bajraan/Sienkiewicz_LED/__QR/Github.Sienkiewicz_LED.png

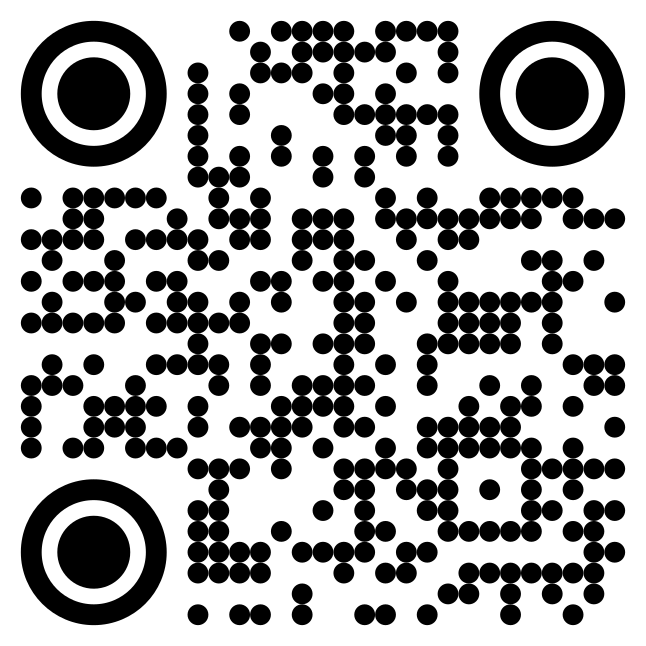
__QR/Github.Sienkiewicz_LED.png
