bajraan/Sienkiewicz_LED/HTML/images/cat_pdf_drill_map_Sienkiewicz_LED-PTH_drill_map.png

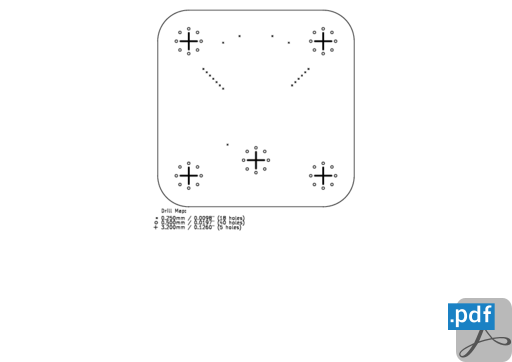
HTML/images/cat_pdf_drill_map_Sienkiewicz_LED-PTH_drill_map.png
