bajraan/Sienkiewicz_LED/HTML/images/cat_png_3d_viewer_angled_top_Sienkiewicz_LED-angled_top.png

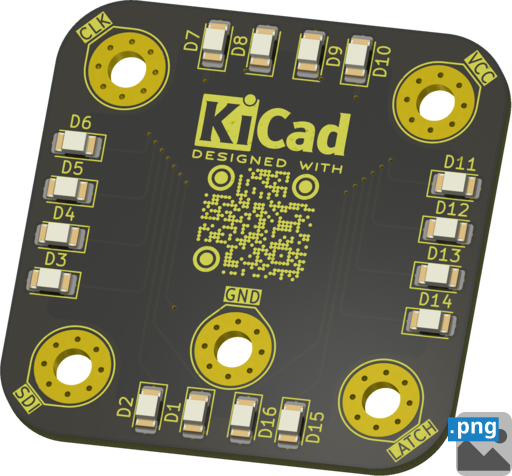
HTML/images/cat_png_3d_viewer_angled_top_Sienkiewicz_LED-angled_top.png
