bajraan/Sienkiewicz_LED/HTML/images/cat_png_3d_viewer_top_Sienkiewicz_LED-top.png

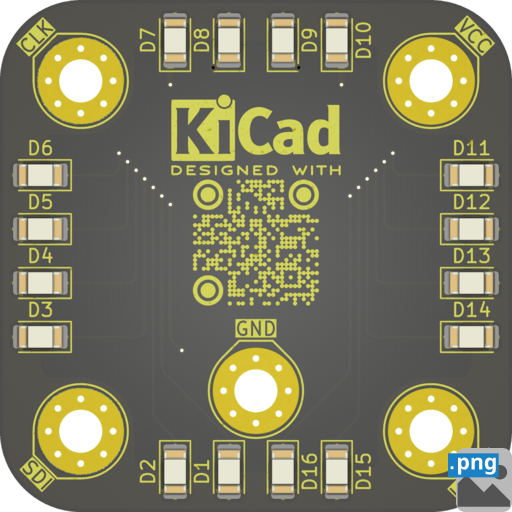
HTML/images/cat_png_3d_viewer_top_Sienkiewicz_LED-top.png
