bajraan/Sienkiewicz_LED/Manufacturing/Assembly/Sienkiewicz_LED-assembly.pdf

# 3ART13 LED Assembly Document

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

BaJRan imgaginary industries

Top/Bottom View

# Top Assembly (Scale 1:1)

# 3ART13 LED Assembly Document


# Bottom Assembly (Scale 1:1)

# 3ART13 LED Assembly Document

Git; Hash:; c7cddf3; Comments:; Sheet Path:; Sheet Title:; File Name:; 3ART13 LED; Sienkiewicz; Company:; CHECKED; Variant:; Board Name:; Sienkiewicz_LED.kicad_pcb; Paweł Baran; Designer:; Reviewer:; Project Name:; Date:; 2.1.1+ (Unreleased); Revision:; Size:; Sheet:; STP16CP05M; 3ART13; SIENKIEWICZ; imaginary industries; BaJRan

BaJRan imgaginary industries

Bottom Assembly (Scale 1:1)
