bajraan/Sienkiewicz_LED/Manufacturing/Fabrication/Sienkiewicz_LED-fabrication-1.pdf

# Top Fabrication (Scale 1:1)

# 3ART13 LED Fabrication Document

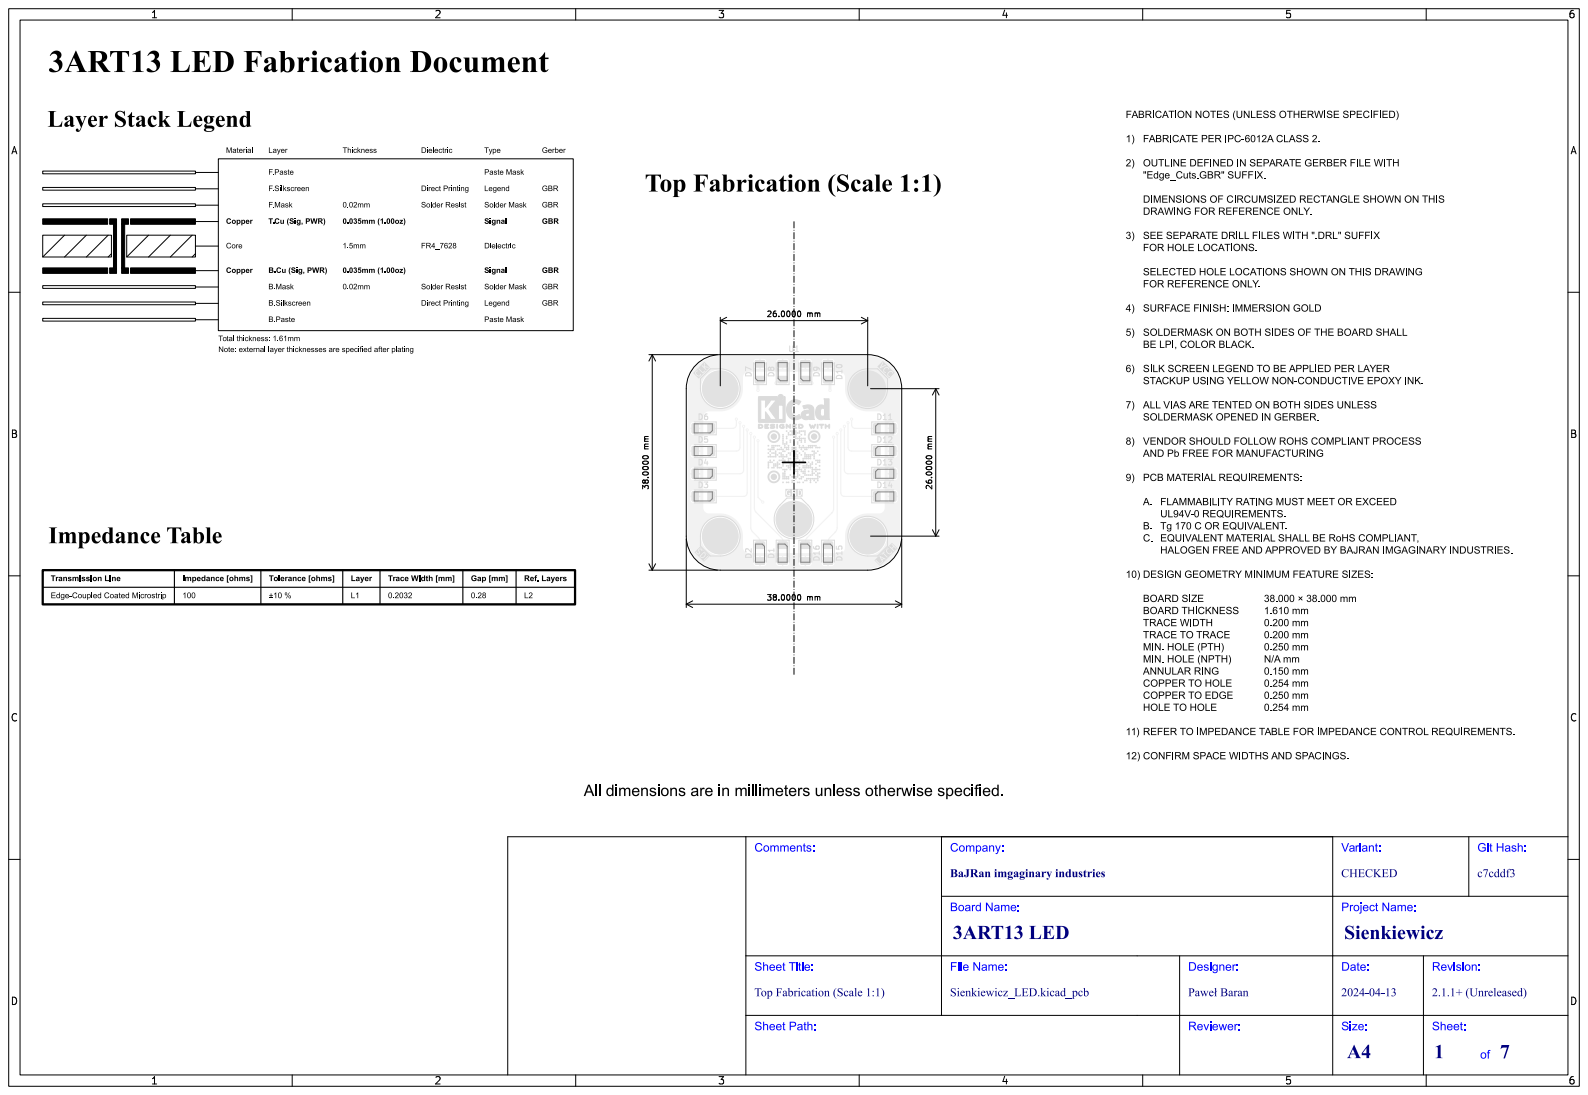
[picture p25: page 1]
