bajraan/Sienkiewicz_LED/Manufacturing/Fabrication/Sienkiewicz_LED-fabrication-3.pdf

# Drill Drawing L1 - L2 (Scale 1:1)

# 3ART13 LED Fabrication Document

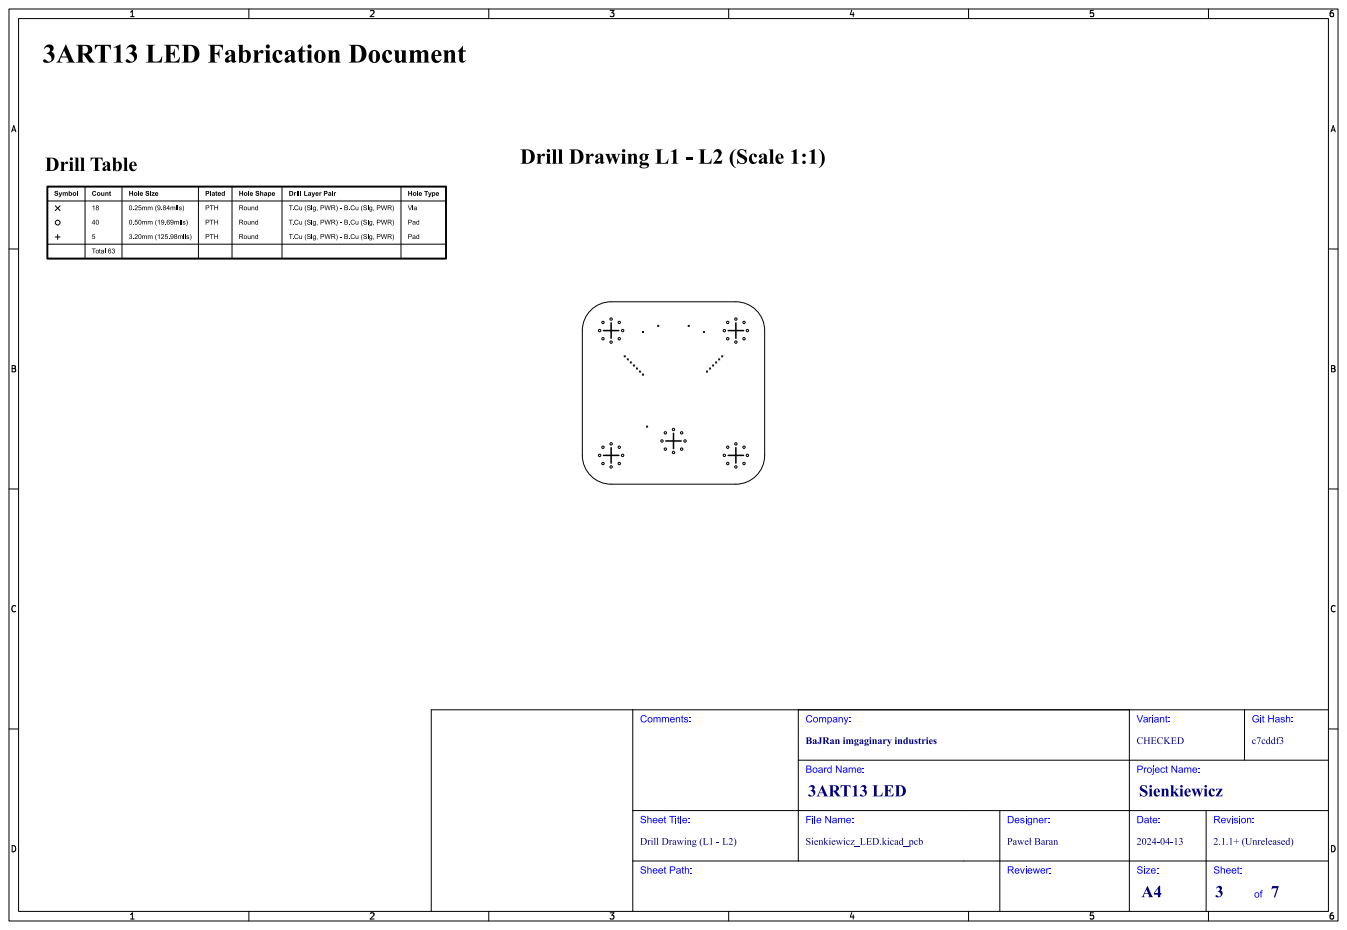
[picture p27: page 1]
Git; Hash:; c7cddf3; Comments:; Drill Drawing (L1 - L2); Sheet Path:; Sheet Title:; File Name:; 3ART13 LED; Sienkiewicz; Company:; CHECKED; Variant:; Board Name:; Sienkiewicz_LED.kicad_pcb; Paweł Baran; Designer:; Reviewer:; Project Name:; Date:; 2.1.1+ (Unreleased); Revision:; Size:; Sheet: 3

BaJRan imgaginary industries
