bajraan/Sienkiewicz_LED/Manufacturing/Fabrication/Sienkiewicz_LED-fabrication-4.pdf

# Top Test Points (Scale 1:1)

# 3ART13 LED Fabrication Document

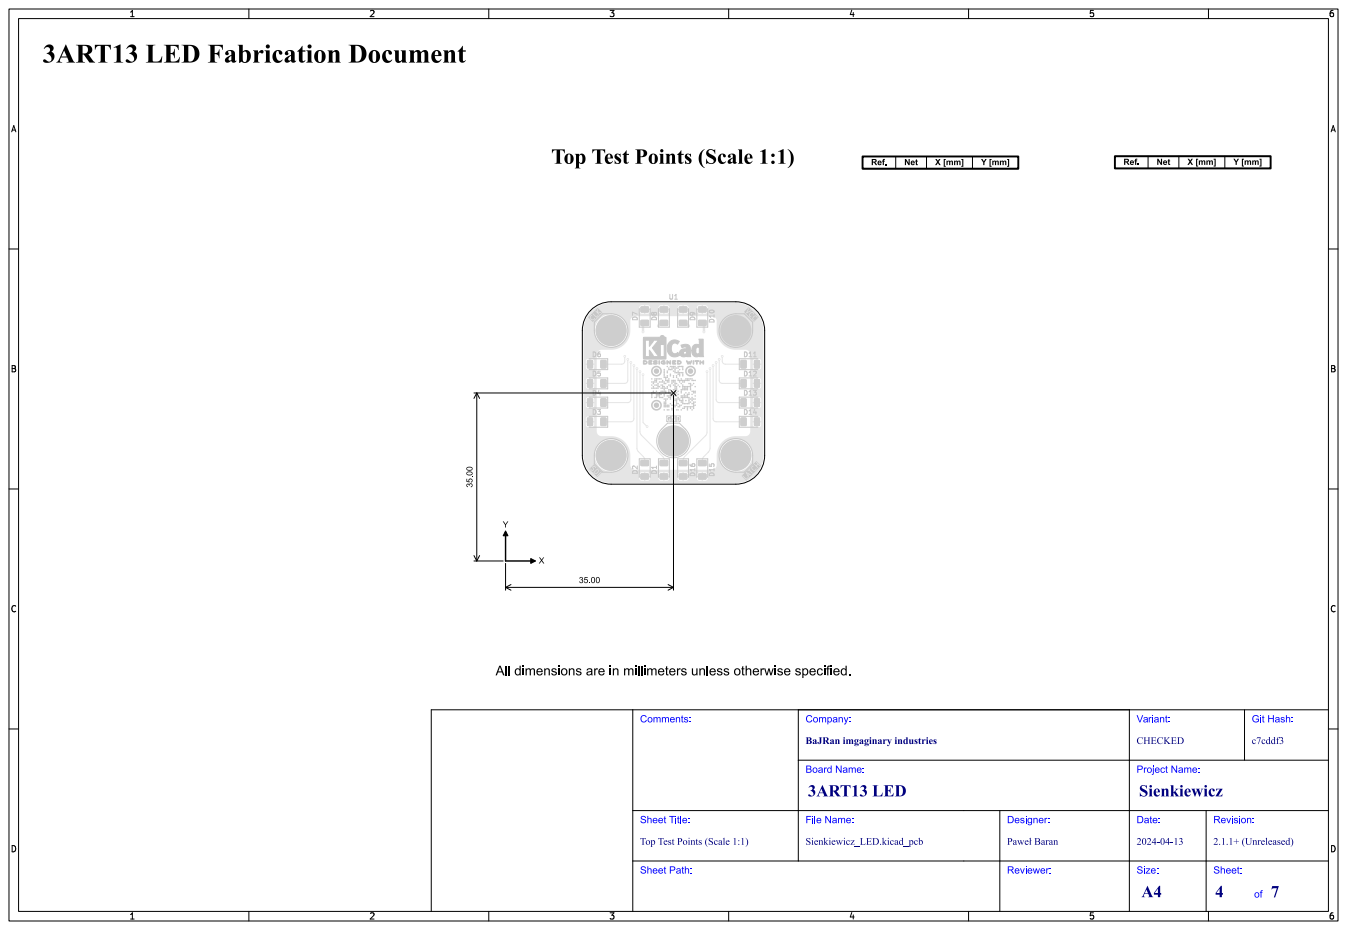
[picture p28: page 1]

Top Test Points (Scale 1:1)
