bajraan/Sienkiewicz_LED/Manufacturing/Fabrication/Sienkiewicz_LED-fabrication-5.pdf

# Bottom Test Points (Scale 1:1)

# 3ART13 LED Fabrication Document

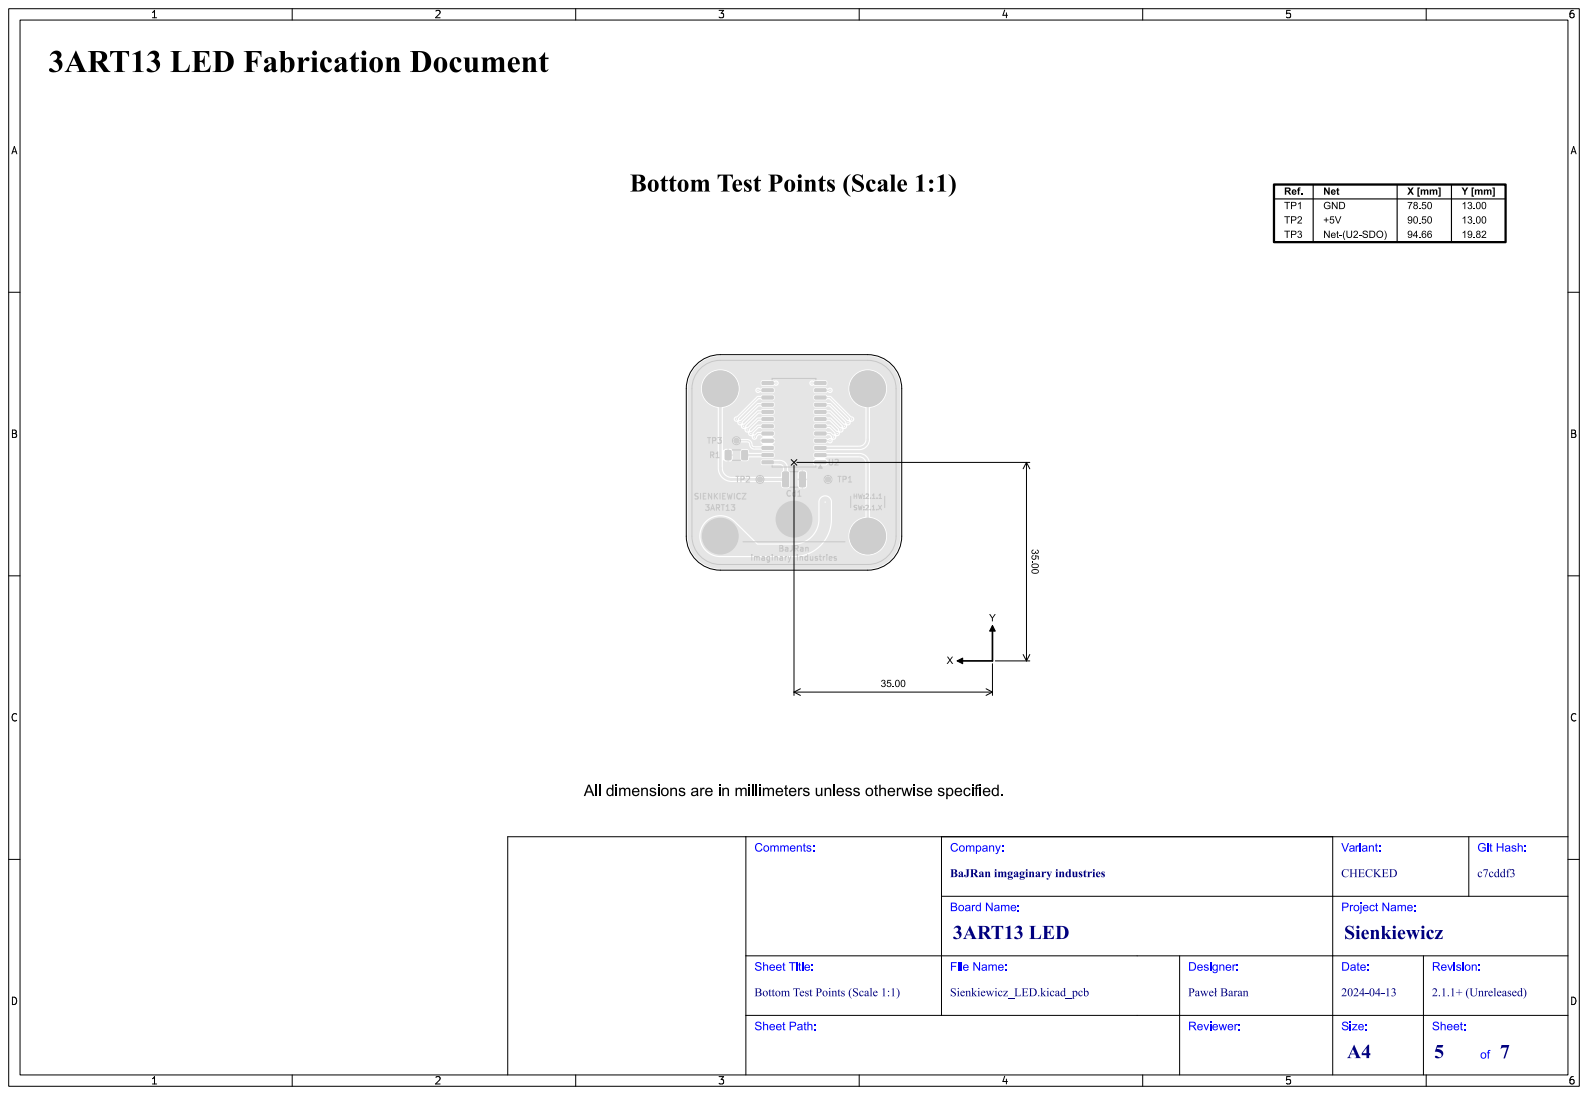
[picture p29: page 1]
Git; Hash:; c7cddf3; Comments:; Sheet Path:; Sheet Title:; File Name:; 3ART13 LED; Sienkiewicz; Company:; CHECKED; Variant:; Board Name:; Sienkiewicz_LED.kicad_pcb; Paweł Baran; Designer:; Reviewer:; Project Name:; Date:; 2.1.1+ (Unreleased); Revision:; Size:; Sheet: 5; 3ART13; SIENKIEWICZ; imaginary; industries; BaJRan

BaJRan imgaginary industries

Bottom Test Points (Scale 1:1)
