bajraan/Sienkiewicz_LED/Manufacturing/Fabrication/Sienkiewicz_LED-fabrication-6.pdf

# T.Cu (Sig, PWR) (Scale 1:1)

# 3ART13 LED Fabrication Document

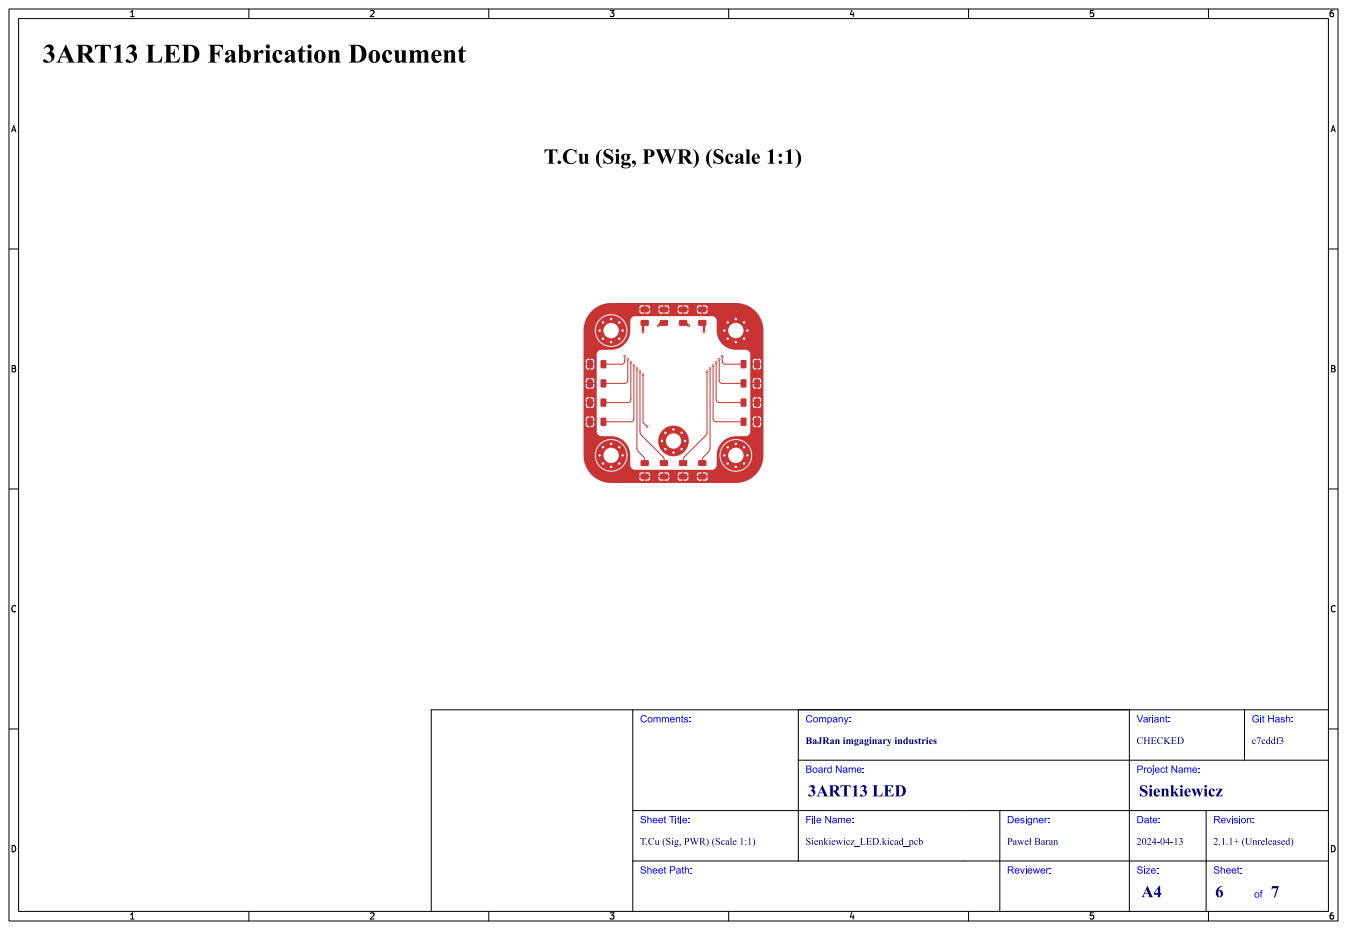
[picture p30: page 1]
Git; Hash:; c7cddf3; Comments:; Sheet Path:; Sheet Title:; File Name:; 3ART13 LED; Sienkiewicz; Company:; CHECKED; Variant:; Board Name:; Sienkiewicz_LED.kicad_pcb; Paweł Baran; Designer:; Reviewer:; Project Name:; Date:; 2.1.1+ (Unreleased); Revision:; Size:; Sheet: 6

BaJRan imgaginary industries

T.Cu (Sig, PWR) (Scale 1:1)
