bajraan/Sienkiewicz_LED/Manufacturing/Fabrication/Sienkiewicz_LED-fabrication-7.pdf

# B.Cu (Sig, PWR) (Scale 1:1)

# 3ART13 LED Fabrication Document

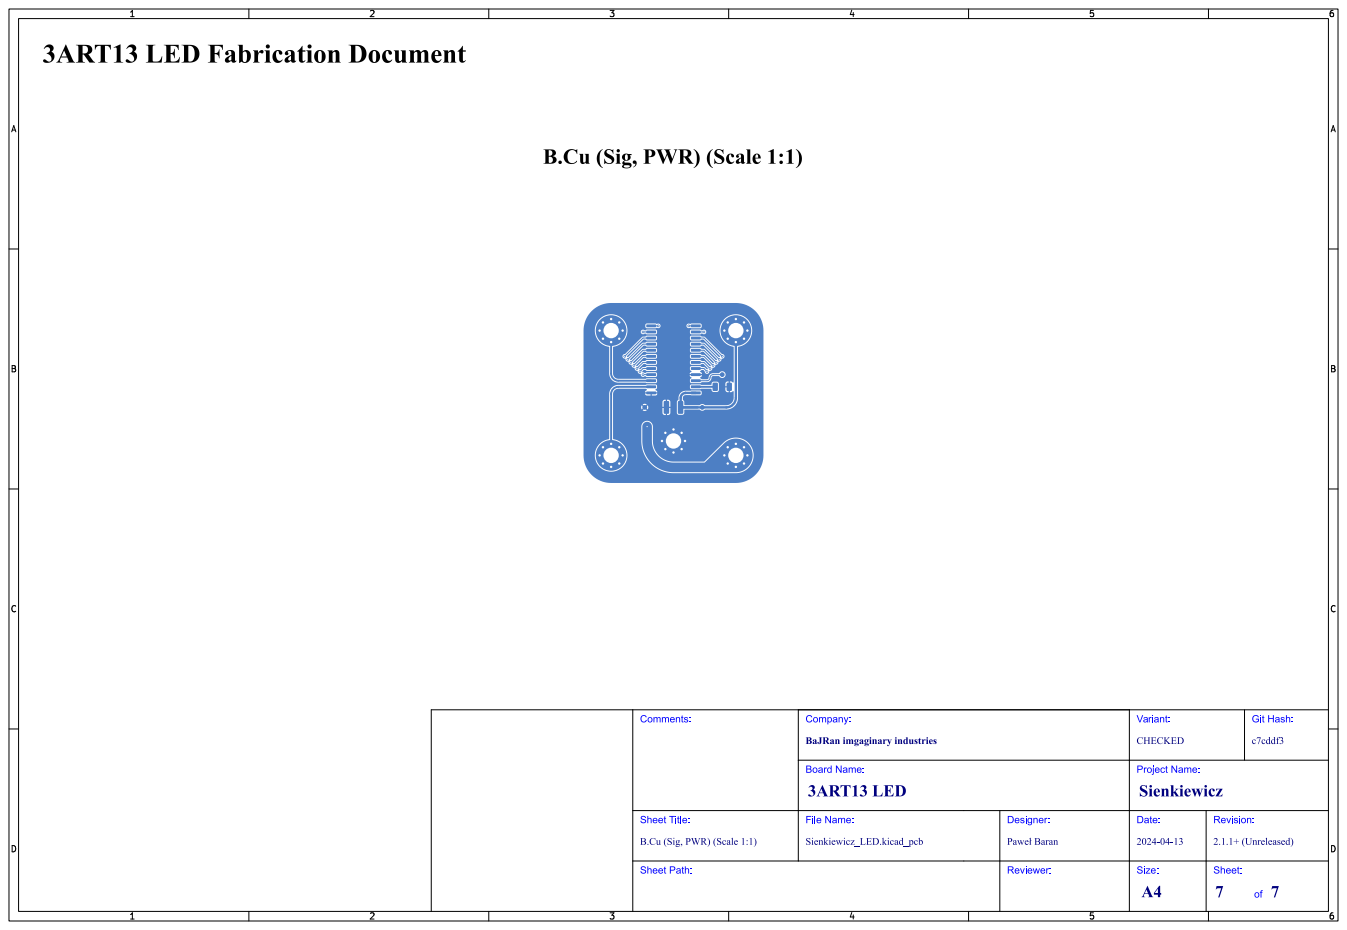
[picture p31: page 1]
Git; Hash:; c7cddf3; Comments:; Sheet Path:; Sheet Title:; File Name:; 3ART13 LED; Sienkiewicz; Company:; CHECKED; Variant:; Board Name:; Sienkiewicz_LED.kicad_pcb; Paweł Baran; Designer:; Reviewer:; Project Name:; Date:; 2.1.1+ (Unreleased); Revision:; Size:; Sheet: 7

BaJRan imgaginary industries

B.Cu (Sig, PWR) (Scale 1:1)
