bajraan/Sienkiewicz_LED/Manufacturing/Fabrication/Sienkiewicz_LED-fabrication.pdf

# Top Fabrication (Scale 1:1)

# 3ART13 LED Fabrication Document


# Bottom Fabrication (Scale 1:1)

# 3ART13 LED Fabrication Document

Git; Hash:; c7cddf3; Comments:; Sheet Path:; Sheet Title:; File Name:; 3ART13 LED; Sienkiewicz; Company:; CHECKED; Variant:; Board Name:; Sienkiewicz_LED.kicad_pcb; Paweł Baran; Designer:; Reviewer:; Project Name:; Date:; 2.1.1+ (Unreleased); Revision:; Size:; Sheet:; 3ART13; SIENKIEWICZ; imaginary industries; BaJRan

BaJRan imgaginary industries

Bottom Fabrication (Scale 1:1)

# Drill Drawing L1 - L2 (Scale 1:1)

# 3ART13 LED Fabrication Document

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

BaJRan imgaginary industries

# Top Test Points (Scale 1:1)

# 3ART13 LED Fabrication Document


Top Test Points (Scale 1:1)

# Bottom Test Points (Scale 1:1)

# 3ART13 LED Fabrication Document

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

BaJRan imgaginary industries

Bottom Test Points (Scale 1:1)

# T.Cu (Sig, PWR) (Scale 1:1)

# 3ART13 LED Fabrication Document

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

BaJRan imgaginary industries

T.Cu (Sig, PWR) (Scale 1:1)

# B.Cu (Sig, PWR) (Scale 1:1)

# 3ART13 LED Fabrication Document

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

BaJRan imgaginary industries

B.Cu (Sig, PWR) (Scale 1:1)
