bajraan/Sienkiewicz_LED/Manufacturing/Fabrication/Gerbers/Sienkiewicz_LED-NPTH_drill_map.pdf

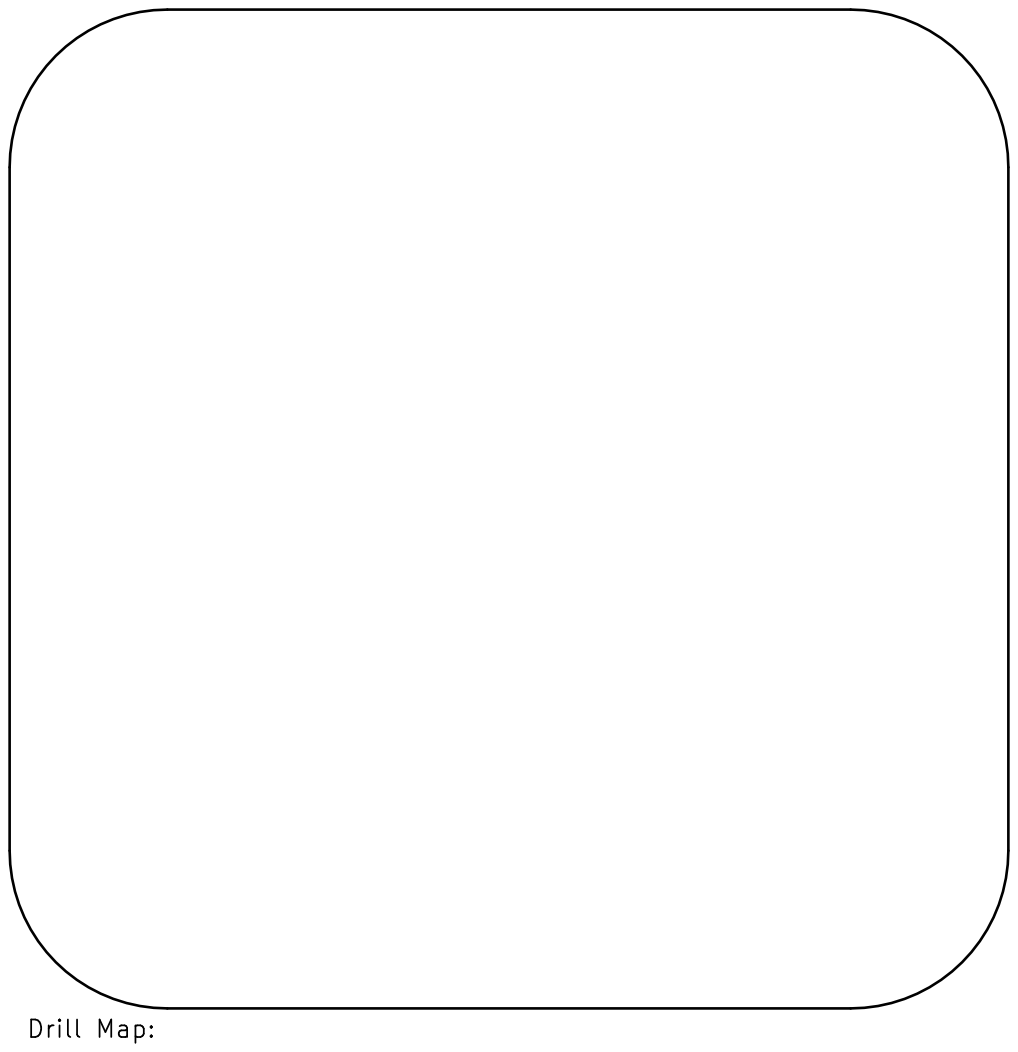
[picture p32: page 1]
