bajraan/Sienkiewicz_LED/Manufacturing/Fabrication/Gerbers/Sienkiewicz_LED-PTH_drill_map.pdf

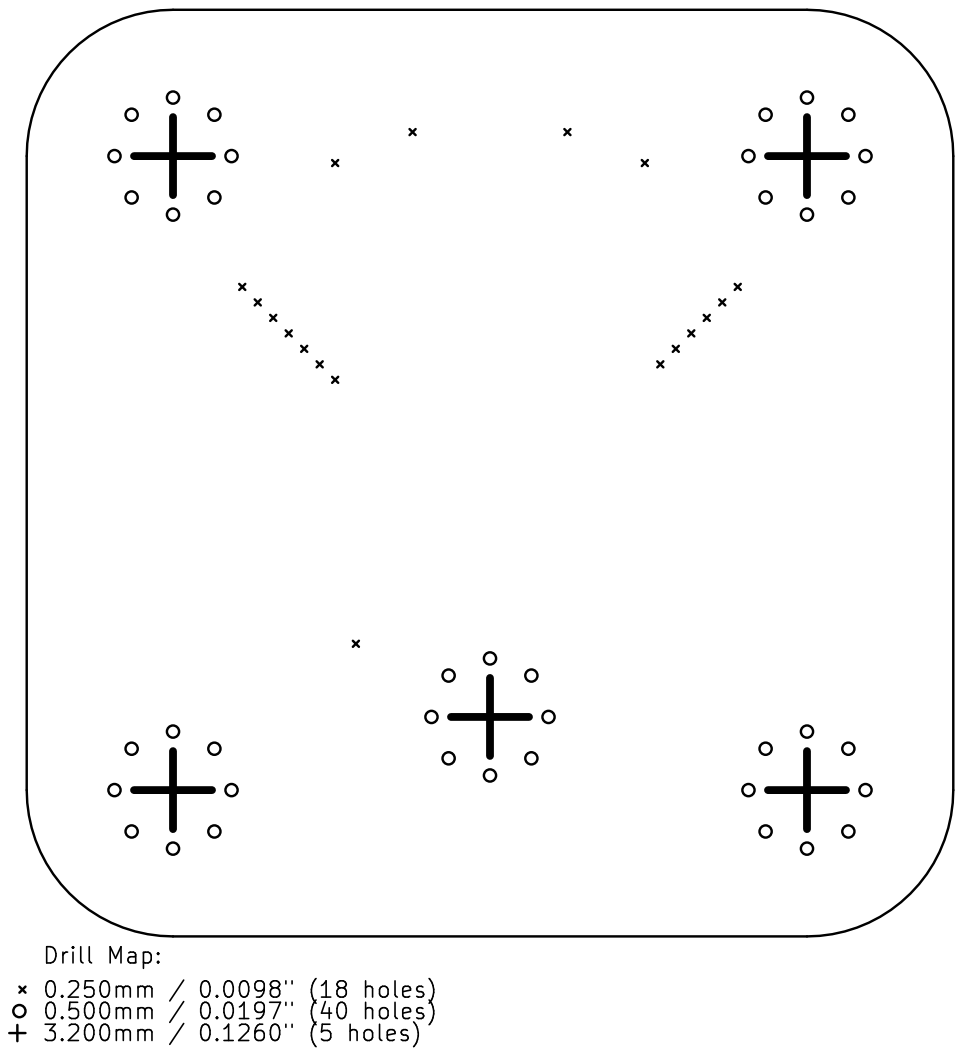
[picture p33: page 1]
